vives-project-xp/MotionTracking/Documentatie/images/20260226_154433.jpg

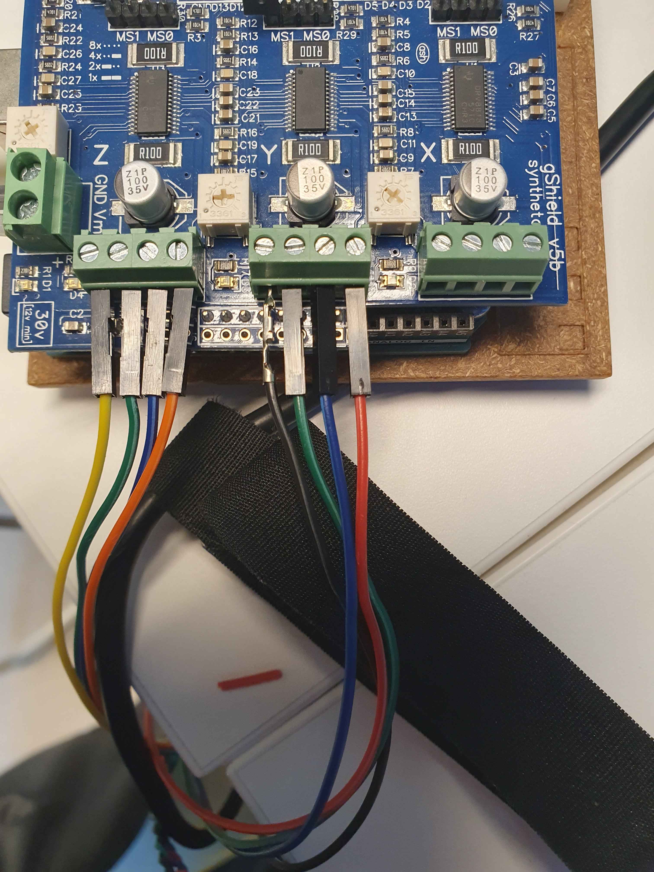
Documentatie/images/20260226_154433.jpg
