vives-project-xp/MotionTracking/Documentatie/images/20260402_152033.jpg

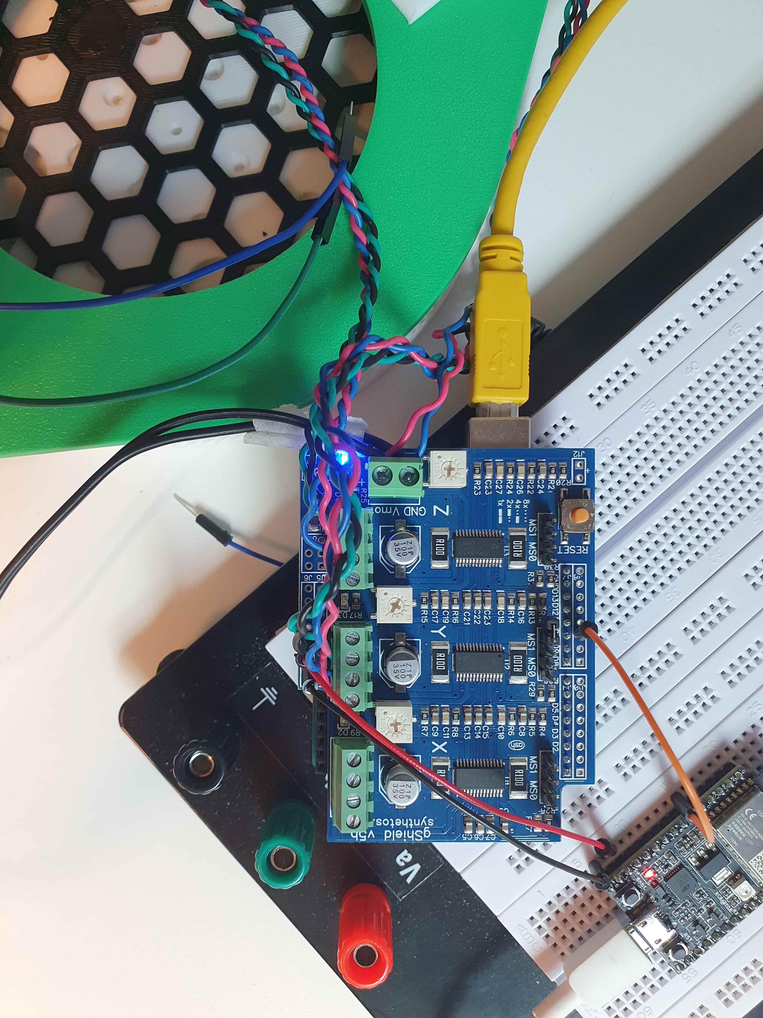
Documentatie/images/20260402_152033.jpg
