vives-project-xp/MotionTracking/Media/image_movingspot.jpg

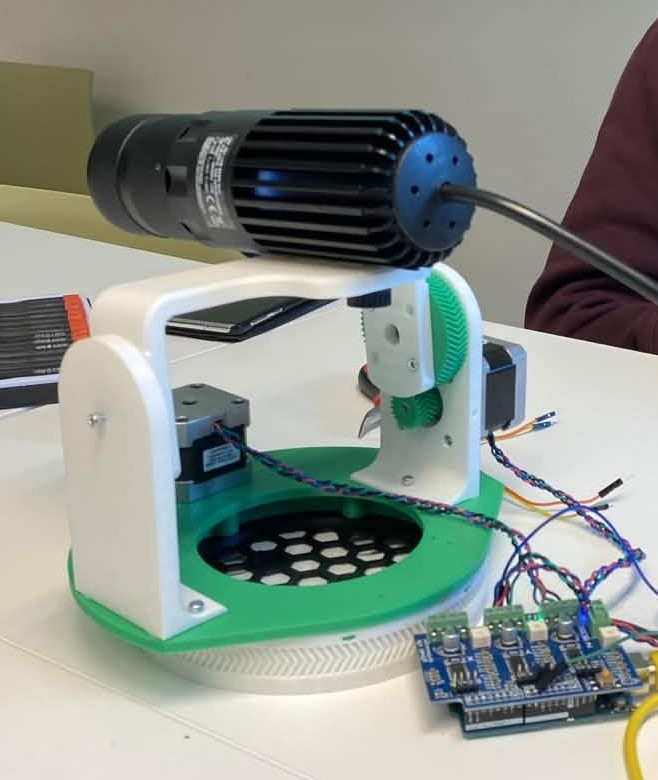
Media/image_movingspot.jpg
