vives-project-xp/MotionTracking/Software/Visual_output/Markers/marker0.png

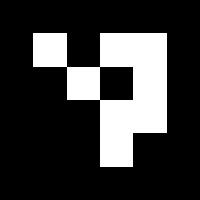
Software/Visual_output/Markers/marker0.png
