vives-project-xp/MotionTracking/Software/Visual_output/Markers/marker1.png

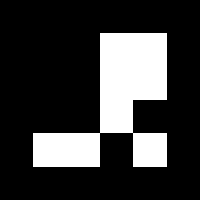
Software/Visual_output/Markers/marker1.png
