vives-project-xp/MotionTracking/Software/Visual_output/Markers/marker2.png

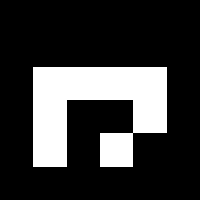
Software/Visual_output/Markers/marker2.png
