vives-project-xp/MotionTracking/Software/Visual_output/Markers/marker3.png

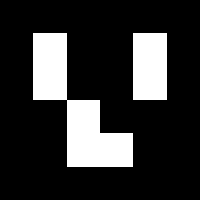
Software/Visual_output/Markers/marker3.png
