vives-project-xp/MotionTracking/Archief/3Dfiles/Printed/Gear_Side_Bearing_Mount.stl

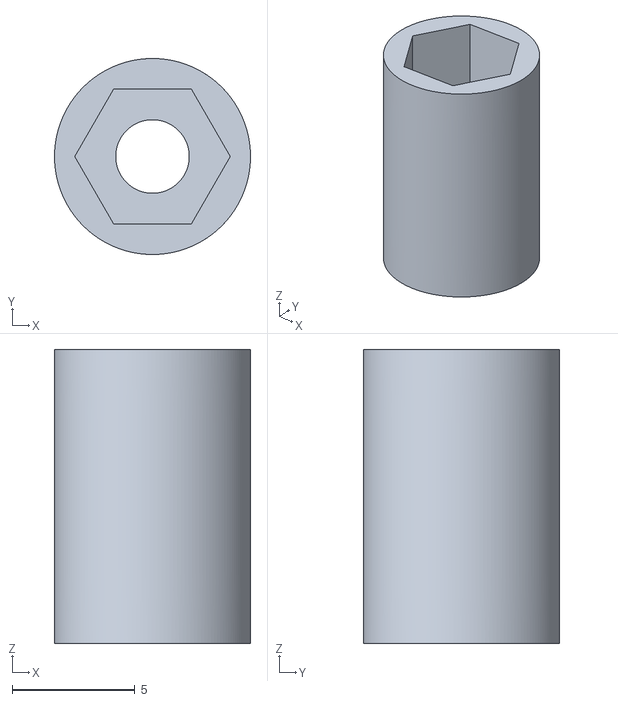
[picture p29: CAD file, 2026-02-26]
Archief/3Dfiles/Printed/Gear_Side_Bearing_Mount.stl
8.00 x 8.00 x 12.0
