vives-project-xp/MotionTracking/Archief/3Dfiles/Printed/Idle_Side_Bearing_Mount.stl

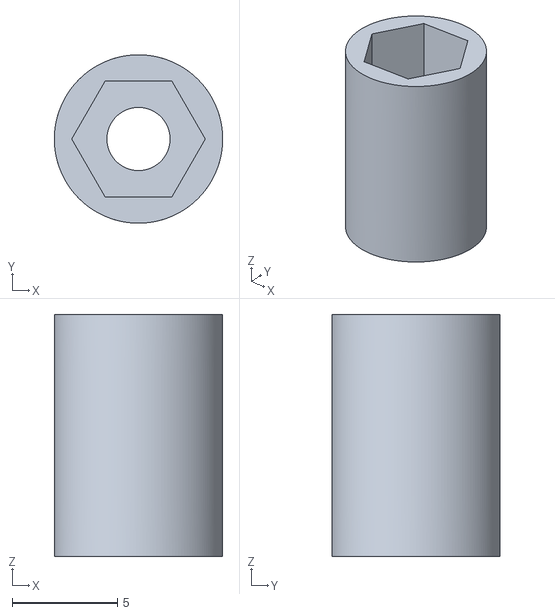
[picture p30: CAD file, 2026-02-26]
Archief/3Dfiles/Printed/Idle_Side_Bearing_Mount.stl
8.00 x 8.00 x 11.5
