vives-project-xp/MotionTracking/Archief/3Dfiles/Printed/Camera_Mounting_Bolt_Spacer.stl

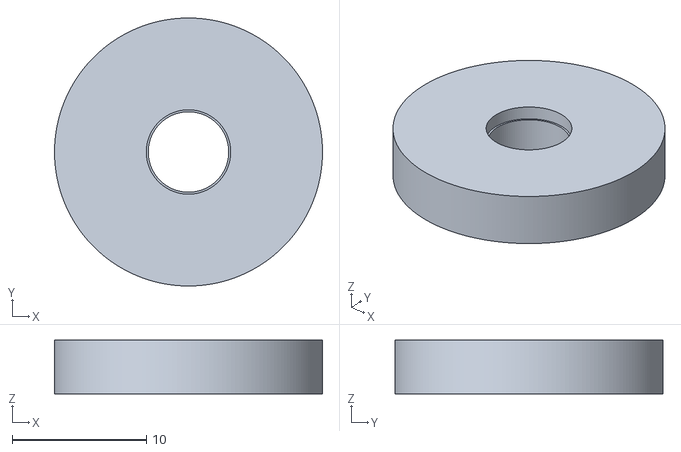
[picture p31: CAD file, 2026-02-26]
Archief/3Dfiles/Printed/Camera_Mounting_Bolt_Spacer.stl
20.0 x 20.0 x 4.00
