vives-project-xp/MotionTracking/Software/Visual_output/Media/formule_kalibratie.png

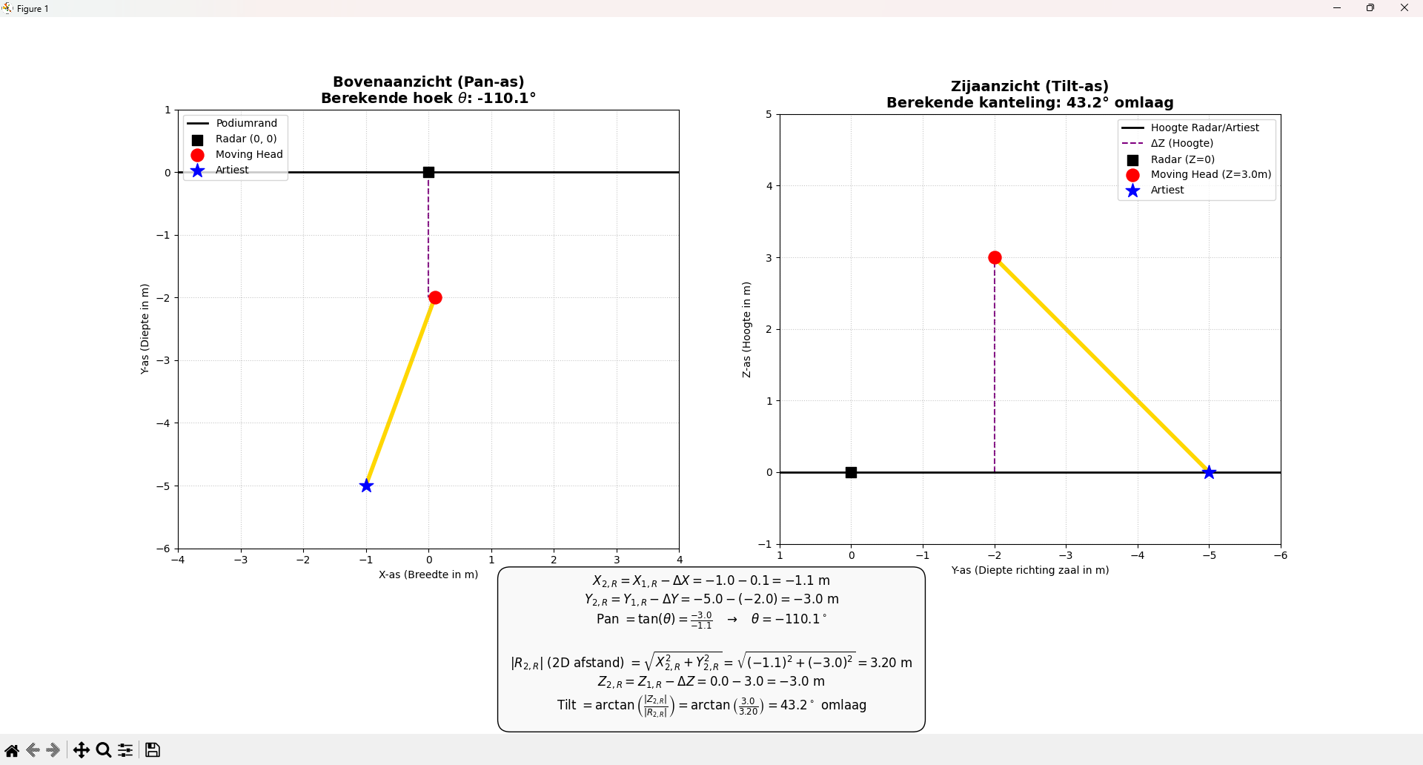
Software/Visual_output/Media/formule_kalibratie.png
