vives-project-xp/MotionTracking/Software/Hailo_tracking/hailo_apps/hailo_app_python/core/gstreamer/gstreamer_app.py

import multiprocessing
from pathlib import Path
import setproctitle
import signal
import os
import gi
import threading
import sys
import cv2
import numpy as np
import time
import queue
gi.require_version('Gst', '1.0')
from gi.repository import Gst, GLib, GObject

# hailo_app_python/core/gstreamer/gstreamer_app.py

# Absolute import for your local helper
from hailo_apps.hailo_app_python.core.gstreamer.gstreamer_helper_pipelines import (
    get_source_type,
)

# Absolute imports for your common utilities
from hailo_apps.hailo_app_python.core.common.defines import (
    HAILO_RGB_VIDEO_FORMAT,
    GST_VIDEO_SINK,
    TAPPAS_POSTPROC_PATH_KEY,
    RESOURCES_PATH_KEY,
    RESOURCES_ROOT_PATH_DEFAULT,
    RESOURCES_VIDEOS_DIR_NAME,
    BASIC_PIPELINES_VIDEO_EXAMPLE_NAME,
    USB_CAMERA,
    RPI_NAME_I,
)
from hailo_apps.hailo_app_python.core.common.camera_utils import (
    get_usb_video_devices,
)
from hailo_apps.hailo_app_python.core.common.core import (
    load_environment,
)
from hailo_apps.hailo_app_python.core.common.buffer_utils import (
    get_caps_from_pad,
    get_numpy_from_buffer,
)


try:
    from picamera2 import Picamera2
except ImportError:
    pass # Available only on Pi OS

# -----------------------------------------------------------------------------------------------
# User-defined class to be used in the callback function
# -----------------------------------------------------------------------------------------------
# A sample class to be used in the callback function
# This example allows to:
# 1. Count the number of frames
# 2. Setup a multiprocessing queue to pass the frame to the main thread
# Additional variables and functions can be added to this class as needed
class app_callback_class:
    def __init__(self):
        self.frame_count = 0
        self.use_frame = False
        self.frame_queue = multiprocessing.Queue(maxsize=3)
        self.running = True

    def increment(self):
        self.frame_count += 1

    def get_count(self):
        return self.frame_count

    def set_frame(self, frame):
        if not self.frame_queue.full():
            self.frame_queue.put(frame)

    def get_frame(self):
        if not self.frame_queue.empty():
            return self.frame_queue.get()
        else:
            return None

def dummy_callback(pad, info, user_data):
    """
    A minimal dummy callback function that returns immediately.

    Args:
        pad: The GStreamer pad
        info: The probe info
        user_data: User-defined data passed to the callback

    Returns:
        Gst.PadProbeReturn.OK
    """
    return Gst.PadProbeReturn.OK

# -----------------------------------------------------------------------------------------------
# GStreamerApp class
# -----------------------------------------------------------------------------------------------
class GStreamerApp:
    def __init__(self, args, user_data: app_callback_class):
        # Set the process title
        setproctitle.setproctitle("Hailo Python App")

        # Create options menu
        self.options_menu = args.parse_args()

        # Set up signal handler for SIGINT (Ctrl-C)
        signal.signal(signal.SIGINT, self.shutdown)

        # Load environment variables
        x=os.environ.get("HAILO_ENV_FILE")
        load_environment(x)

        # Initialize variables
        tappas_post_process_dir = Path(os.environ.get(TAPPAS_POSTPROC_PATH_KEY, ''))
        if tappas_post_process_dir == '':
            print("TAPPAS_POST_PROC_DIR environment variable is not set. Please set it by running set-env in cli")
            exit(1)
        self.current_path = os.path.dirname(os.path.abspath(__file__))
        self.postprocess_dir = tappas_post_process_dir
        if self.options_menu.input is None:
            self.video_source = str(Path(RESOURCES_ROOT_PATH_DEFAULT) / RESOURCES_VIDEOS_DIR_NAME / BASIC_PIPELINES_VIDEO_EXAMPLE_NAME)
        else:
            self.video_source = self.options_menu.input
        if self.video_source == USB_CAMERA:
            self.video_source = get_usb_video_devices()
            if not self.video_source:
                print('Provided argument "--input" is set to "usb", however no available USB cameras found. Please connect a camera or specifiy different input method.')
                exit(1)
            else:
                self.video_source = self.video_source[0]
        self.source_type = get_source_type(self.video_source)
        self.frame_rate = self.options_menu.frame_rate
        self.user_data = user_data
        self.video_sink = GST_VIDEO_SINK
        self.pipeline = None
        self.loop = None
        self.threads = []
        self.error_occurred = False
        self.pipeline_latency = 300  # milliseconds

        # Set Hailo parameters; these parameters should be set based on the model used
        self.batch_size = 1
        self.video_width = 1280
        self.video_height = 720
        self.video_format = HAILO_RGB_VIDEO_FORMAT
        self.hef_path = None
        self.app_callback = None

        # Set user data parameters
        user_data.use_frame = self.options_menu.use_frame

        self.sync = "false" if (self.options_menu.disable_sync or self.source_type != "file") else "true"
        self.show_fps = self.options_menu.show_fps

        if self.options_menu.dump_dot:
            os.environ["GST_DEBUG_DUMP_DOT_DIR"] = os.getcwd()
        
        self.webrtc_frames_queue = None  # for appsink & GUI mode

    def appsink_callback(self, appsink):
        """
        Callback function for the appsink element in the GStreamer pipeline.
        This function is called when a new sample (frame) is available in the appsink (output from the pipeline).
        """
        sample = appsink.emit('pull-sample')
        if sample:
            buffer = sample.get_buffer()
            if buffer:
                format, width, height = get_caps_from_pad(appsink.get_static_pad("sink"))
                frame = get_numpy_from_buffer(buffer, format, width, height)
                frame = cv2.cvtColor(frame, cv2.COLOR_BGR2RGB)  # convert from BGR to RGB
                try:
                    self.webrtc_frames_queue.put(frame)  # Add the frame to the queue (non-blocking)
                except queue.Full:
                    print("Frame queue is full. Dropping frame.")  # Drop the frame if the queue is full
        return Gst.FlowReturn.OK

    def on_fps_measurement(self, sink, fps, droprate, avgfps):
        print(f"FPS: {fps:.2f}, Droprate: {droprate:.2f}, Avg FPS: {avgfps:.2f}")
        return True

    def create_pipeline(self):
        # Initialize GStreamer
        Gst.init(None)

        pipeline_string = self.get_pipeline_string()
        try:
            self.pipeline = Gst.parse_launch(pipeline_string)
        except Exception as e:
            print(f"Error creating pipeline: {e}", file=sys.stderr)
            sys.exit(1)

        # Connect to hailo_display fps-measurements
        if self.show_fps:
            print("Showing FPS")
            self.pipeline.get_by_name("hailo_display").connect("fps-measurements", self.on_fps_measurement)

        # Create a GLib Main Loop
        self.loop = GLib.MainLoop()

    def bus_call(self, bus, message, loop):
        t = message.type
        if t == Gst.MessageType.EOS:
            print("End-of-stream")
            self.on_eos()
        elif t == Gst.MessageType.ERROR:
            err, debug = message.parse_error()
            print(f"Error: {err}, {debug}", file=sys.stderr)
            self.error_occurred = True
            self.shutdown()
        # QOS
        elif t == Gst.MessageType.QOS:
            # Handle QoS message here
            # If lots of QoS messages are received, it may indicate that the pipeline is not able to keep up
            if not hasattr(self, 'qos_count'):
                self.qos_count = 0
            self.qos_count += 1
            if self.qos_count > 50 and self.qos_count % 10 == 0:
                qos_element = message.src.get_name()
                print(f"\033[91mQoS message received from {qos_element}\033[0m")
                print(f"\033[91mLots of QoS messages received: {self.qos_count}, consider optimizing the pipeline or reducing the pipeline frame rate see '--frame-rate' flag.\033[0m")

        return True




    def on_eos(self):
        if self.source_type == "file":
            if self.sync == "false":
                # Pause the pipeline to clear any queued data. It is required when running with sync=false
                # This will produce some warnings, but it's fine
                print("Pausing pipeline for rewind... some warnings are expected.")
                self.pipeline.set_state(Gst.State.PAUSED)
            
            # Seek to the beginning (position 0) using a flush seek.
            success = self.pipeline.seek_simple(Gst.Format.TIME, Gst.SeekFlags.FLUSH, 0)
            if success:
                print("Video rewound successfully. Restarting playback...")
            else:
                print("Error rewinding video.", file=sys.stderr)

            # Resume playback.
            self.pipeline.set_state(Gst.State.PLAYING)
        else:
            self.shutdown()


    def shutdown(self, signum=None, frame=None):
        print("Shutting down... Hit Ctrl-C again to force quit.")
        signal.signal(signal.SIGINT, signal.SIG_DFL)
        self.pipeline.set_state(Gst.State.PAUSED)
        GLib.usleep(100000)  # 0.1 second delay

        self.pipeline.set_state(Gst.State.READY)
        GLib.usleep(100000)  # 0.1 second delay

        self.pipeline.set_state(Gst.State.NULL)
        GLib.idle_add(self.loop.quit)
   
    def update_fps_caps(self, new_fps=30, source_name='source'):
        """Updates the FPS by setting max-rate on videorate element directly"""
        # Derive the videorate and capsfilter element names based on the source name
        videorate_name = f"{source_name}_videorate"
        capsfilter_name = f"{source_name}_fps_caps"

        # Get the videorate element
        videorate = self.pipeline.get_by_name(videorate_name)
        if videorate is None:
            print(f"Element {videorate_name} not found in the pipeline.")
            return

        # Print current properties for debugging
        current_max_rate = videorate.get_property("max-rate")
        print(f"Current videorate max-rate: {current_max_rate}")

        # Update the max-rate property directly
        videorate.set_property("max-rate", new_fps)

        # Verify the change
        updated_max_rate = videorate.get_property("max-rate")
        print(f"Updated videorate max-rate to: {updated_max_rate}")

        # Get the capsfilter element
        capsfilter = self.pipeline.get_by_name(capsfilter_name)
        if capsfilter:
            new_caps_str = f"video/x-raw, framerate={new_fps}/1"
            new_caps = Gst.Caps.from_string(new_caps_str)
            capsfilter.set_property("caps", new_caps)
            print(f"Updated capsfilter caps to match new rate")

        # Update frame_rate property
        self.frame_rate = new_fps


    def get_pipeline_string(self):
        # This is a placeholder function that should be overridden by the child class
        return ""

    def dump_dot_file(self):
        print("Dumping dot file...")
        Gst.debug_bin_to_dot_file(self.pipeline, Gst.DebugGraphDetails.ALL, "pipeline")
        return False

    def run(self):
        # Add a watch for messages on the pipeline's bus
        bus = self.pipeline.get_bus()
        bus.add_signal_watch()
        bus.connect("message", self.bus_call, self.loop)


        # Connect pad probe to the identity element
        if not self.options_menu.disable_callback:
            identity = self.pipeline.get_by_name("identity_callback")
            if identity is None:
                print("Warning: identity_callback element not found, add <identity name=identity_callback> in your pipeline where you want the callback to be called.")
            else:
                identity_pad = identity.get_static_pad("src")
                identity_pad.add_probe(Gst.PadProbeType.BUFFER, self.app_callback, self.user_data)

        hailo_display = self.pipeline.get_by_name("hailo_display")
        if hailo_display is None and not getattr(self.options_menu, 'ui', False):
            print("Warning: hailo_display element not found, add <fpsdisplaysink name=hailo_display> to your pipeline to support fps display.")

        # Disable QoS to prevent frame drops
        disable_qos(self.pipeline)

        # Start a subprocess to run the display_user_data_frame function
        if self.options_menu.use_frame:
            display_process = multiprocessing.Process(target=display_user_data_frame, args=(self.user_data,))
            display_process.start()

        if self.source_type == RPI_NAME_I:
            picam_thread = threading.Thread(target=picamera_thread, args=(self.pipeline, self.video_width, self.video_height, self.video_format))
            self.threads.append(picam_thread)
            picam_thread.start()

        # Set the pipeline to PAUSED to ensure elements are initialized
        self.pipeline.set_state(Gst.State.PAUSED)

        # Set pipeline latency
        new_latency = self.pipeline_latency * Gst.MSECOND  # Convert milliseconds to nanoseconds
        self.pipeline.set_latency(new_latency)

        # Set pipeline to PLAYING state
        self.pipeline.set_state(Gst.State.PLAYING)

        # Dump dot file
        if self.options_menu.dump_dot:
            GLib.timeout_add_seconds(3, self.dump_dot_file)

        # Run the GLib event loop
        self.loop.run()

        # Clean up
        try:
            self.user_data.running = False
            self.pipeline.set_state(Gst.State.NULL)
            if self.options_menu.use_frame:
                display_process.terminate()
                display_process.join()
            for t in self.threads:
                t.join()
        except Exception as e:
            print(f"Error during cleanup: {e}", file=sys.stderr)
        finally:
            if self.error_occurred:
                print("Exiting with error...", file=sys.stderr)
                sys.exit(1)
            else:
                print("Exiting...")
                sys.exit(0)

def picamera_thread(pipeline, video_width, video_height, video_format, picamera_config=None):
    appsrc = pipeline.get_by_name("app_source")
    appsrc.set_property("is-live", True)
    appsrc.set_property("format", Gst.Format.TIME)
    print("appsrc properties: ", appsrc)
    # Initialize Picamera2
    with Picamera2() as picam2:
        if picamera_config is None:
            # Default configuration
            main = {'size': (1280, 720), 'format': 'RGB888'}
            lores = {'size': (video_width, video_height), 'format': 'RGB888'}
            controls = {'FrameRate': 30}
            config = picam2.create_preview_configuration(main=main, lores=lores, controls=controls)
        else:
            config = picamera_config
        # Configure the camera with the created configuration
        picam2.configure(config)
        # Update GStreamer caps based on 'lores' stream
        lores_stream = config['lores']
        format_str = 'RGB' if lores_stream['format'] == 'RGB888' else video_format
        width, height = lores_stream['size']
        print(f"Picamera2 configuration: width={width}, height={height}, format={format_str}")
        appsrc.set_property(
            "caps",
            Gst.Caps.from_string(
                f"video/x-raw, format={format_str}, width={width}, height={height}, "
                f"framerate=30/1, pixel-aspect-ratio=1/1"
            )
        )
        picam2.start()
        frame_count = 0
        start_time = time.time()
        print("picamera_process started")
        while True:
            frame_data = picam2.capture_array('lores')
            # frame_data = np.random.randint(0, 255, (height, width, 3), dtype=np.uint8)
            if frame_data is None:
                print("Failed to capture frame.")
                break
            # Convert framontigue data if necessary
            frame = cv2.cvtColor(frame_data, cv2.COLOR_BGR2RGB)
            frame = np.asarray(frame)
            # Create Gst.Buffer by wrapping the frame data
            buffer = Gst.Buffer.new_wrapped(frame.tobytes())
            # Set buffer PTS and duration
            buffer_duration = Gst.util_uint64_scale_int(1, Gst.SECOND, 30)
            buffer.pts = frame_count * buffer_duration
            buffer.duration = buffer_duration
            # Push the buffer to appsrc
            ret = appsrc.emit('push-buffer', buffer)
            if ret == Gst.FlowReturn.FLUSHING:
                break
            if ret != Gst.FlowReturn.OK:
                print("Failed to push buffer:", ret)
                break
            frame_count += 1

def disable_qos(pipeline):
    """
    Iterate through all elements in the given GStreamer pipeline and set the qos property to False
    where applicable.
    When the 'qos' property is set to True, the element will measure the time it takes to process each buffer and will drop frames if latency is too high.
    We are running on long pipelines, so we want to disable this feature to avoid dropping frames.
    :param pipeline: A GStreamer pipeline object
    """
    # Ensure the pipeline is a Gst.Pipeline instance
    if not isinstance(pipeline, Gst.Pipeline):
        print("The provided object is not a GStreamer Pipeline")
        return

    # Iterate through all elements in the pipeline
    it = pipeline.iterate_elements()
    while True:
        result, element = it.next()
        if result != Gst.IteratorResult.OK:
            break

        # Check if the element has the 'qos' property
        if 'qos' in GObject.list_properties(element):
            # Set the 'qos' property to False
            element.set_property('qos', False)
            print(f"Set qos to False for {element.get_name()}")

# This function is used to display the user data frame
def display_user_data_frame(user_data: app_callback_class):
    while user_data.running:
        frame = user_data.get_frame()
        if frame is not None:
            cv2.imshow("User Frame", frame)
        cv2.waitKey(1)
    cv2.destroyAllWindows()
